asahikawa-robolab/rotary_encoder_slave/program/odometry.X/setup.h

/*-----------------------------------------------
 *
 * Last updated : 2020/02/02, 15:45
 * Author       : Takuto Jibiki
 *
-----------------------------------------------*/
#ifndef SETUP_H
#define SETUP_H

void setup_dspic(void);
void setup_pin(void);
void setup_peripheral_module(void);

#endif
